ChrisUustal/smartwatch/PCB/395_Smartwatch.sch

## EAGLE design PCB/395_Smartwatch.sch (2021-11-26)

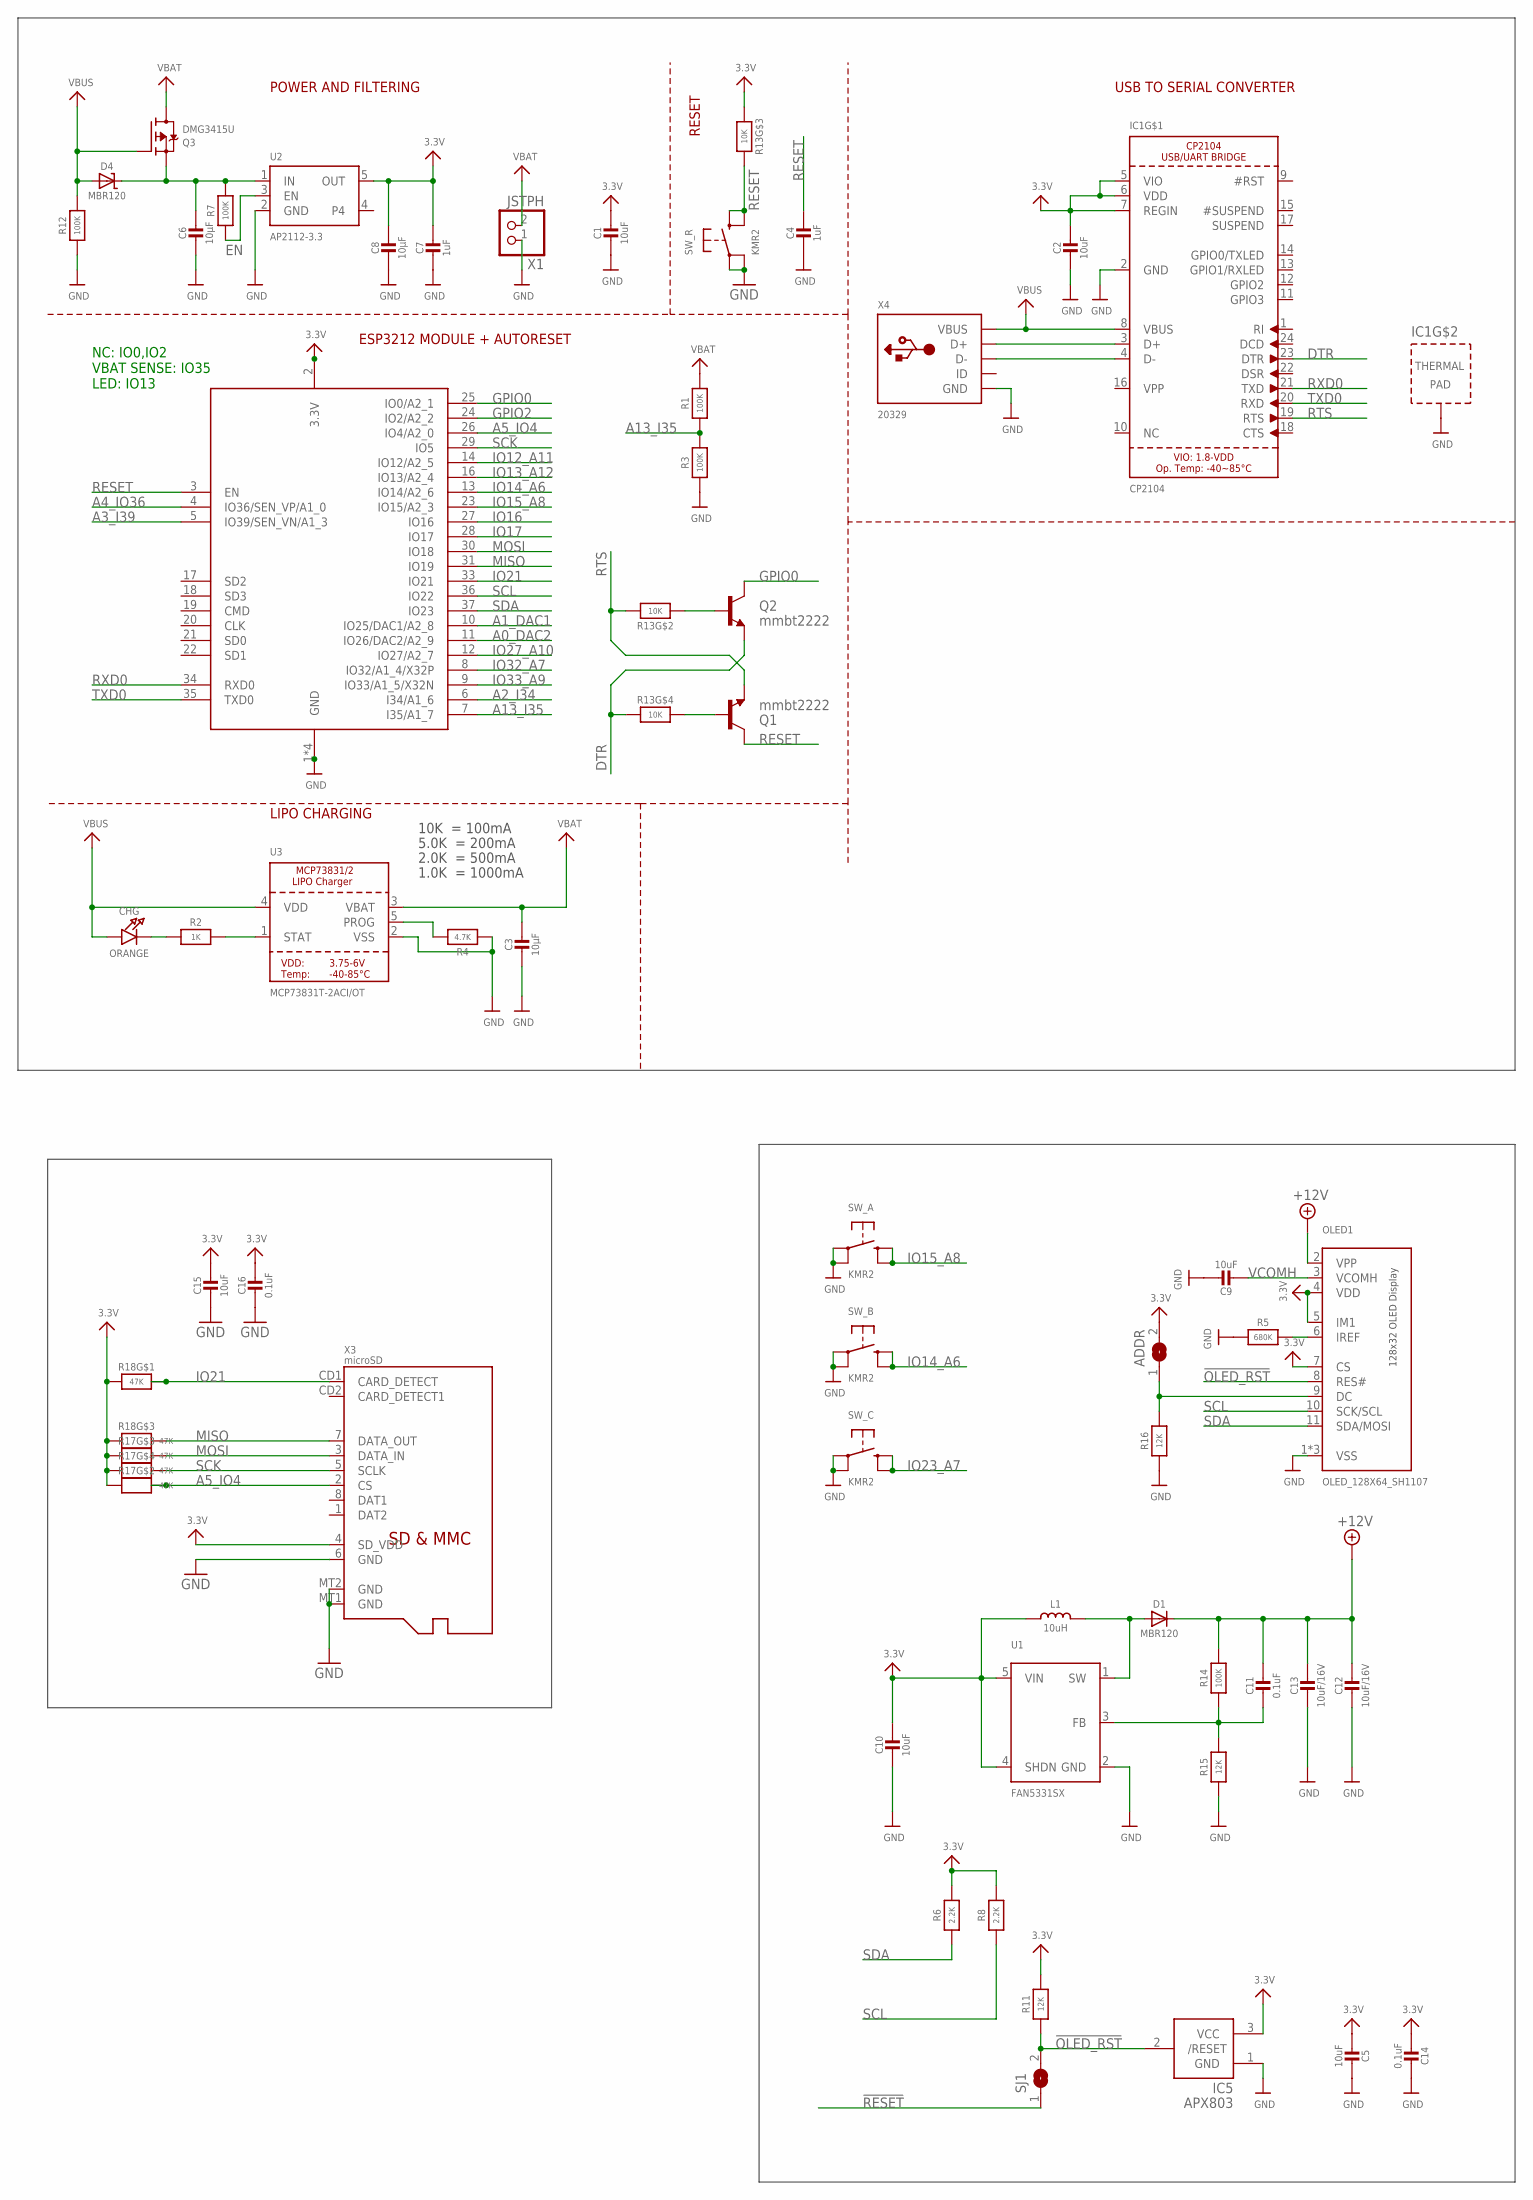
[picture p15: schematic 395_Smartwatch.sch]

Parts:
ADDR: SOLDERJUMPER; SOLDERJUMPER_ARROW_NOPASTE
C1, C2, C5, C9, C10, C15: 10uF; 0805-NO
C3, C6, C8: 10µF; 0805-NO
C4, C7: 1uF; 0603-NO
C11, C14, C16: 0.1uF; 0603-NO
C12, C13: 10uF/16V; 0805-NO
CHG: ORANGE; CHIPLED_0805_NOOUTLINE
D1, D4: MBR120; SOD-123
IC1: CP2104; QFN24_4MM_SMSC
IC5: APX803; SOT23
L1: 10uH; INDUCTOR_1007
OLED1: OLED_128X64_SH1107; QT1107P11A
Q1, Q2: mmbt2222; SOT23-3
Q3: DMG3415U; SOT23-R
R1, R3, R7, R12, R14: 100K; 0603-NO
R2: 1K; 0603-NO
R4: 4.7K; 0603-NO
R5: 680K; 0603-NO
R6, R8: 2.2K; 0603-NO
R11, R15, R16: 12K; 0603-NO
R13: 10K; RESPACK_4X0603
R17, R18: 47K; RESPACK_4X0603
SJ1: SOLDERJUMPERCLOSED; SOLDERJUMPER_CLOSEDWIRE
SW_A: KMR2; BTN_KMR2_4.6X2.8
SW_B: KMR2; BTN_KMR2_4.6X2.8
SW_C: KMR2; BTN_KMR2_4.6X2.8
SW_R: KMR2; BTN_KMR2_4.6X2.8
U1: FAN5331SX; SOT23-5
U2: AP2112-3.3; SOT23-5
U3: MCP73831T-2ACI/OT; SOT23-5
X1: JSTPH; JSTPH2
X2: ESP32_WROOM32_SKINNY; WROOM32_SKINNY
X3: microSD; MICROSD
X4: 20329; 4UCONN_20329_V2

Connections:
3.3V: ADDR.2, C1.1, C2.1, C5.2, C7.1, C8.1, C10.1, C14.2, C15.1, C16.1, IC1.5 (VIO), IC1.6 (VDD), IC1.7 (REGIN), IC5.3 (VCC), L1.P$1 (1), OLED1.4 (VDD), OLED1.5 (IM1), OLED1.7 (CS), R6.2, R8.2, R11.2, R13.3 (1), R17.2 (1), R17.3 (1), R17.4 (1), R18.1, R18.3 (1), U1.4 (SHDN), U1.5 (VIN), U2.5 (OUT), X2.2 (3.3V), X3.4 (SD_VDD)
!OLED_RST: IC5.2 (/RESET), OLED1.8 (RES#), R11.1, SJ1.2
!RESET: SJ1.1
+12V: C11.1, C12.1, C13.1, D1.C, OLED1.2 (VPP), R14.2
A0_DAC2: X2.11 (IO26/DAC2/A2_9)
A1_DAC1: X2.10 (IO25/DAC1/A2_8)
A2_I34: X2.6 (I34/A1_6)
A3_I39: X2.5 (IO39/SEN_VN/A1_3)
A4_IO36: X2.4 (IO36/SEN_VP/A1_0)
A5_IO4: R17.7 (2), X2.26 (IO4/A2_0), X3.2 (CS)
A13_I35: R1.1, R3.2, X2.7 (I35/A1_7)
DTR: IC1.23 (DTR), Q2.2 (E), R13.4 (1)
EN: R7.1, U2.3 (EN)
GND: C1.2, C2.2, C3.2, C4.2, C5.1, C6.2, C7.2, C8.2, C9.1, C10.2, C12.2, C13.2, C14.1, C15.2, C16.2, IC1.2 (GND), IC1.THERM (TP), IC5.1 (GND), OLED1.1 (VSS), R3.1, R4.1, R5.1, R12.1, R15.1, R16.1, SW_A.A, SW_A.A' (P1), SW_B.A, SW_B.A' (P1), SW_C.A, SW_C.A' (P1), SW_R.A, SW_R.A' (P1), U1.2 (GND), U2.2 (GND), U3.2 (VSS), X1.1, X2.1 (GND), X3.6 (GND), X3.MT1 (GND), X3.MT2 (GND), X4.BASE@1 (GND)
GPIO0: Q2.3 (C), X2.25 (IO0/A2_1)
GPIO2: X2.24 (IO2/A2_2)
IO12_A11: X2.14 (IO12/A2_5)
IO13_A12: X2.16 (IO13/A2_4)
IO14_A6: SW_B.B (S), SW_B.B' (S1), X2.13 (IO14/A2_6)
IO15_A8: SW_A.B (S), SW_A.B' (S1), X2.23 (IO15/A2_3)
IO16: X2.27 (IO16)
IO17: X2.28 (IO17)
IO21: R18.8 (2), X2.33 (IO21), X3.CD1 (CARD_DETECT)
IO23_A7: SW_C.B (S), SW_C.B' (S1)
IO27_A10: X2.12 (IO27/A2_7)
IO32_A7: X2.8 (IO32/A1_4/X32P)
IO33_A9: X2.9 (IO33/A1_5/X32N)
MISO: R18.6 (2), X2.31 (IO19), X3.7 (DATA_OUT)
MOSI: R17.6 (2), X2.30 (IO18), X3.3 (DATA_IN)
unnamed: CHG.C, R2.1
unnamed: IC1.3 (D+), X4.D+
unnamed: R2.2, U3.1 (STAT)
unnamed: R4.2, U3.5 (PROG)
unnamed: IC1.4 (D-), X4.D-
unnamed: C6.1, D4.C, Q3.2 (S), R7.2, U2.1 (IN)
unnamed: OLED1.6 (IREF), R5.2
unnamed: D1.A, L1.P$2 (2), U1.1 (SW)
unnamed: C11.2, R14.1, R15.2, U1.3 (FB)
unnamed: ADDR.1, OLED1.9 (DC), R16.2
unnamed: Q1.1 (B), R13.5 (2)
unnamed: Q2.1 (B), R13.2 (1)
RESET: C4.1, Q1.3 (C), R13.6 (2), SW_R.B (S), SW_R.B' (S1), X2.3 (EN)
RTS: IC1.19 (RTS), Q1.2 (E), R13.7 (2)
RXD0: IC1.21 (TXD), X2.34 (RXD0)
SCK: R17.5 (2), X2.29 (IO5), X3.5 (SCLK)
SCL: OLED1.10 (SCK/SCL), R8.1, X2.36 (IO22)
SDA: OLED1.11 (SDA/MOSI), R6.1, X2.37 (IO23)
TXD0: IC1.20 (RXD), X2.35 (TXD0)
VBAT: C3.1, Q3.3 (D), R1.2, U3.3 (VBAT), X1.2
VBUS: CHG.A, D4.A, IC1.8 (VBUS), Q3.1 (G), R12.2, U3.4 (VDD), X4.VBUS
VCOMH: C9.2, OLED1.3 (VCOMH)

Notes on the sheet:
POWER AND FILTERING
RESET
10K = 100mA
5.0K = 200mA
2.0K = 500mA
1.0K = 1000mA
USB TO SERIAL CONVERTER
LIPO CHARGING
ESP3212 MODULE + AUTORESET
NC: IO0,IO2 VBAT SENSE: IO35 LED: IO13
