ChrisUustal/smartwatch/smartwatch/settings.h

//settings.h
#ifndef SETTINGS_H
#define SETTINGS_H

void settings_setup();
void settings_display_adv();
void settings_scroll_event();
void settings_select_event();
void print_setting_selector(settings_fsm_enum state);

#endif
